sbarry753/cse123/max78000/README.md

# MAX78000 Platform Testing

Testing MAX78000FTHR as alternative platform for real-time polyphonic detection.

## Status
- Development environment: Set up complete
- Example code: Located and studied complete
- Hardware: Obtaining this week in progress
- Testing: Pending hardware in progress

## Examples
- `examples/I2S_DMA/` - Reference code for audio passthrough implementation

## Next Steps
1. Flash example to board when hardware arrives
2. Modify for audio passthrough
3. Benchmark performance
4. Compare to other results
