sbarry753/cse123/Documentation/aesthetic_prototype/topDownView.png

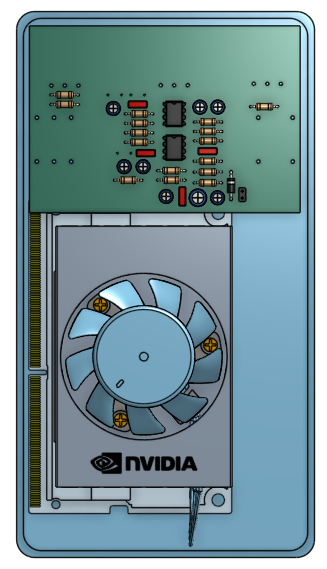
Documentation/aesthetic_prototype/topDownView.png
