sbarry753/cse123/Documentation/images/Guitar Pedal.drawio.png

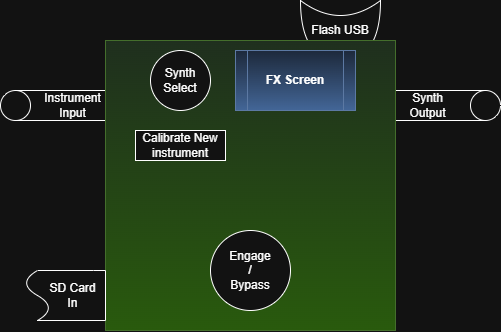
Documentation/images/Guitar Pedal.drawio.png
