sbarry753/cse123/Documentation/images/LUTPolyphonic.drawio (1).png

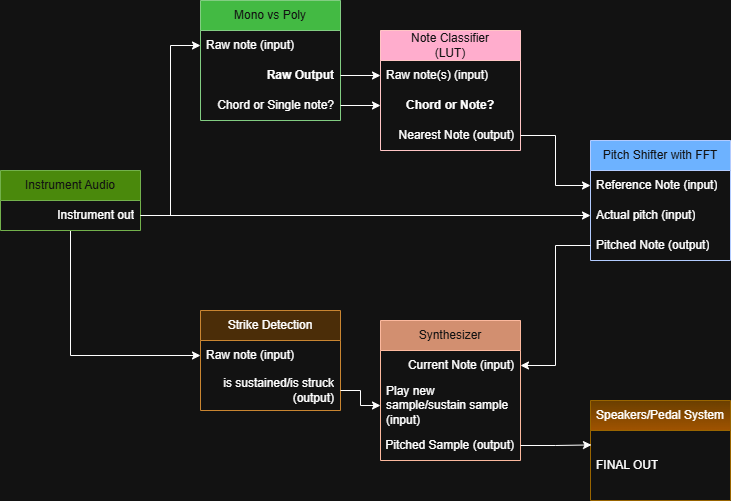
Documentation/images/LUTPolyphonic.drawio (1).png
