sbarry753/cse123/Documentation/images/pcm_signal.png

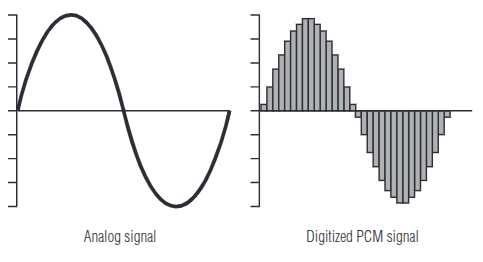
Documentation/images/pcm_signal.png
