sbarry753/cse123/Documentation/images/pedalAsciiArt.png

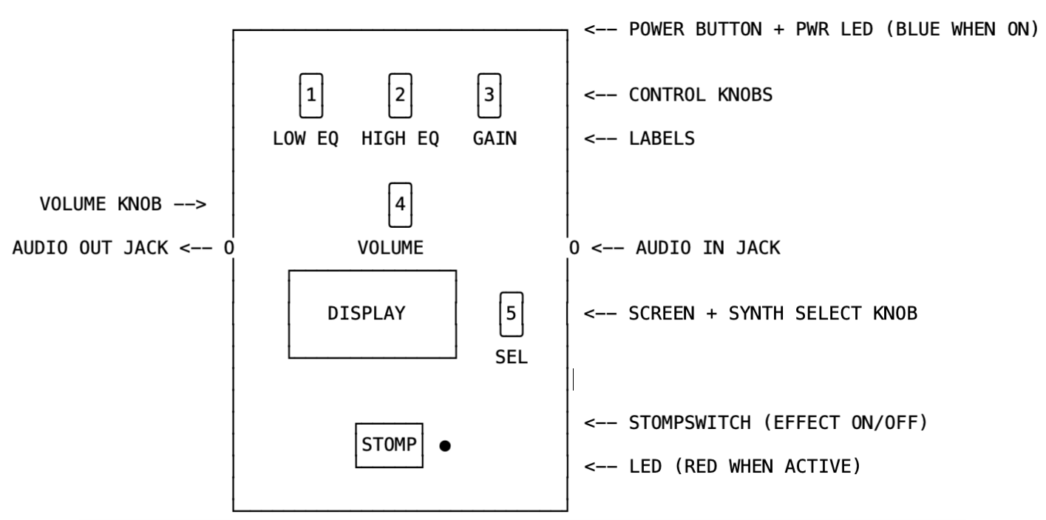
Documentation/images/pedalAsciiArt.png
