sbarry753/cse123/LUT - In Development/Notes on guitar.png

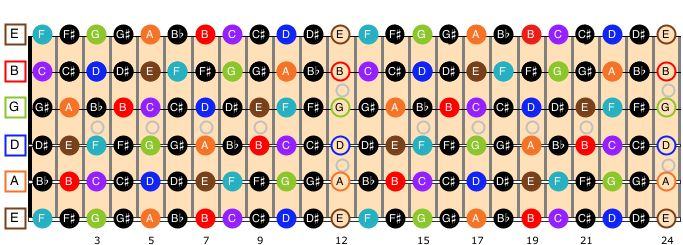
LUT - In Development/Notes on guitar.png
