sbarry753/cse123/NET - In Development/semitone_comparison.png

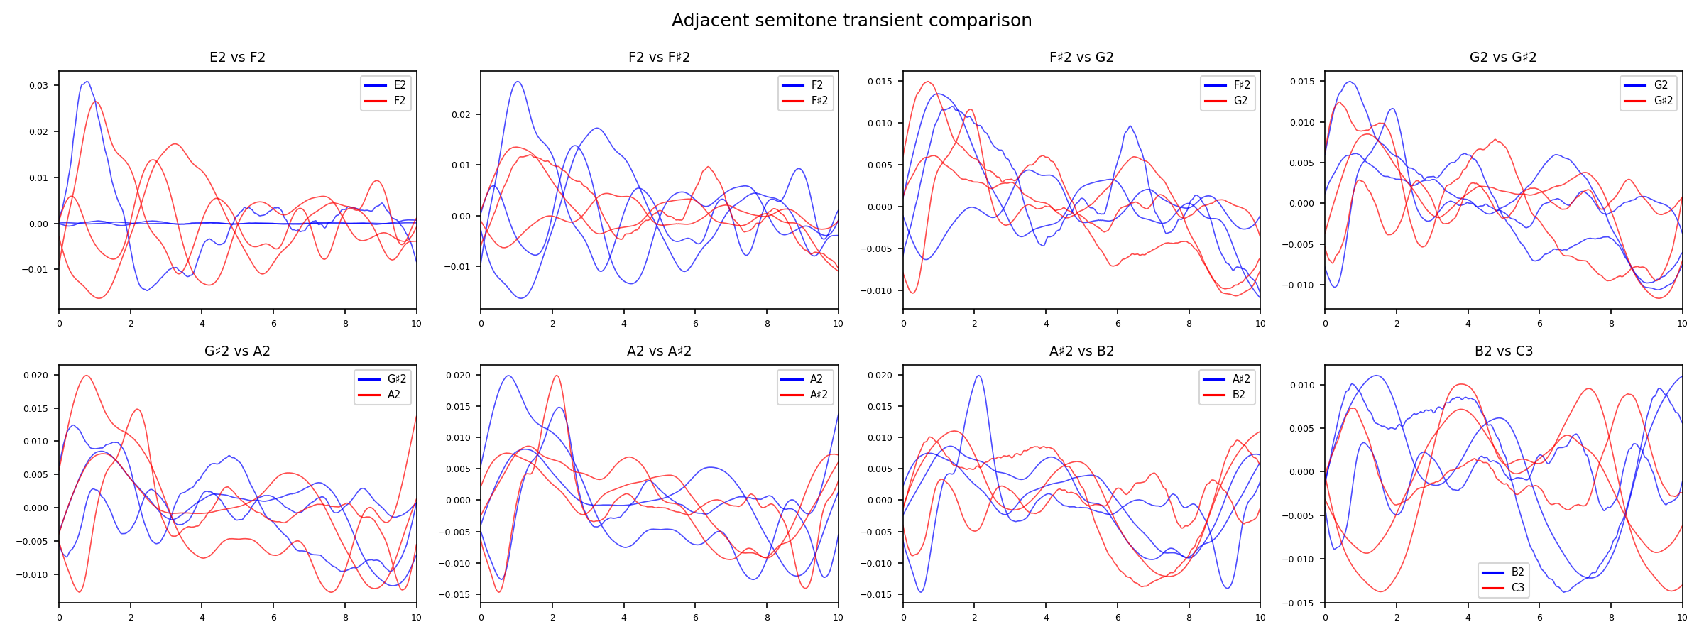
NET - In Development/semitone_comparison.png
