sbarry753/cse123/NET - In Development/transient_inspection.png

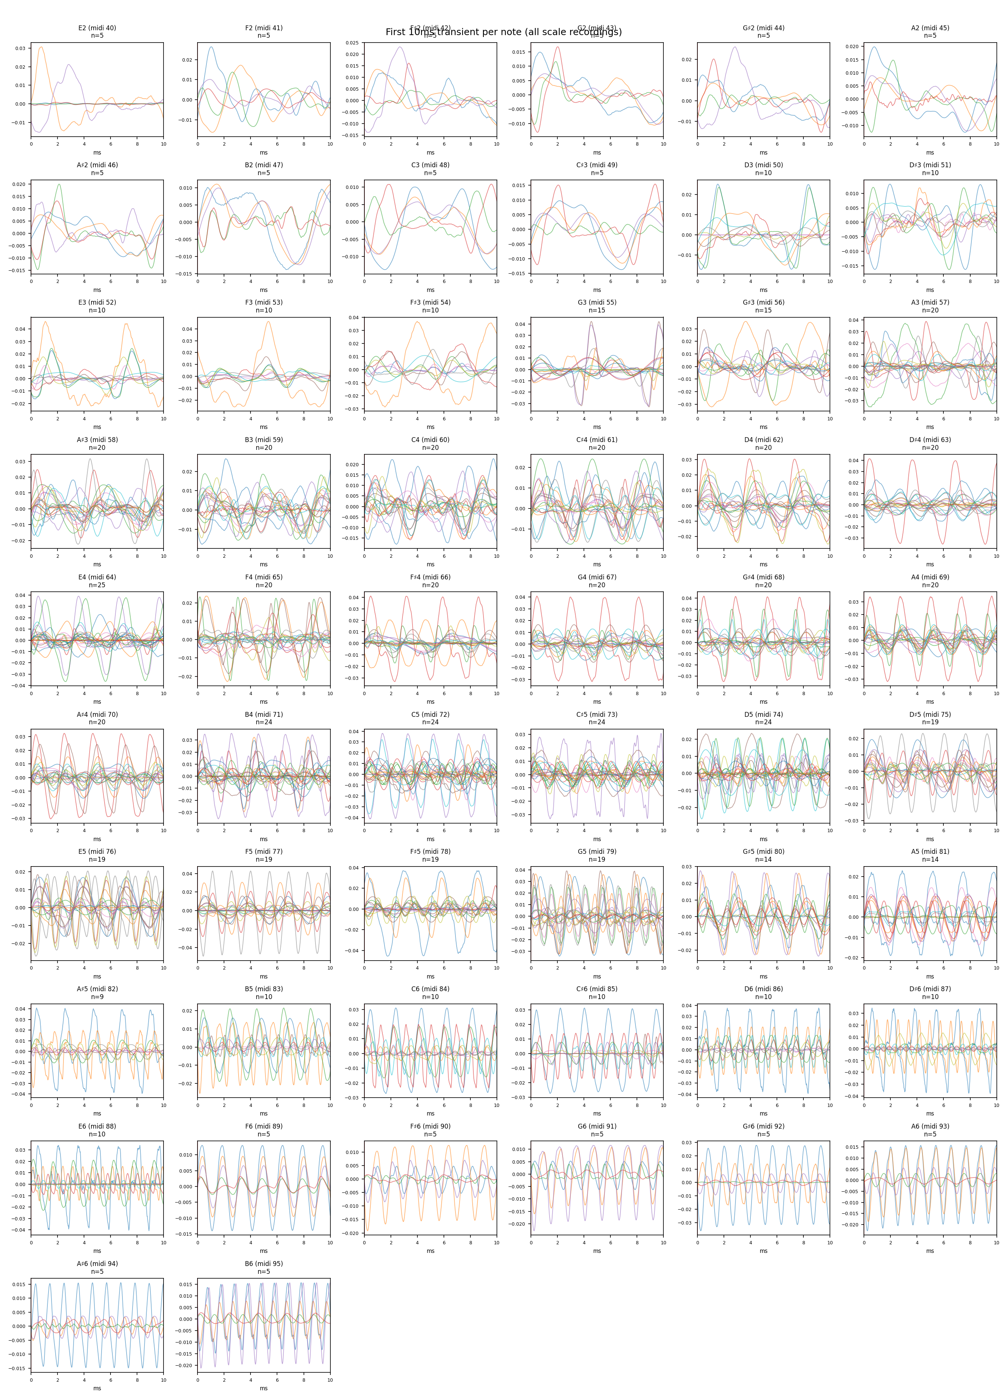
NET - In Development/transient_inspection.png
