sbarry753/cse123/special_effects/test_files/Downloads/LUTPolyphonic.drawio.png

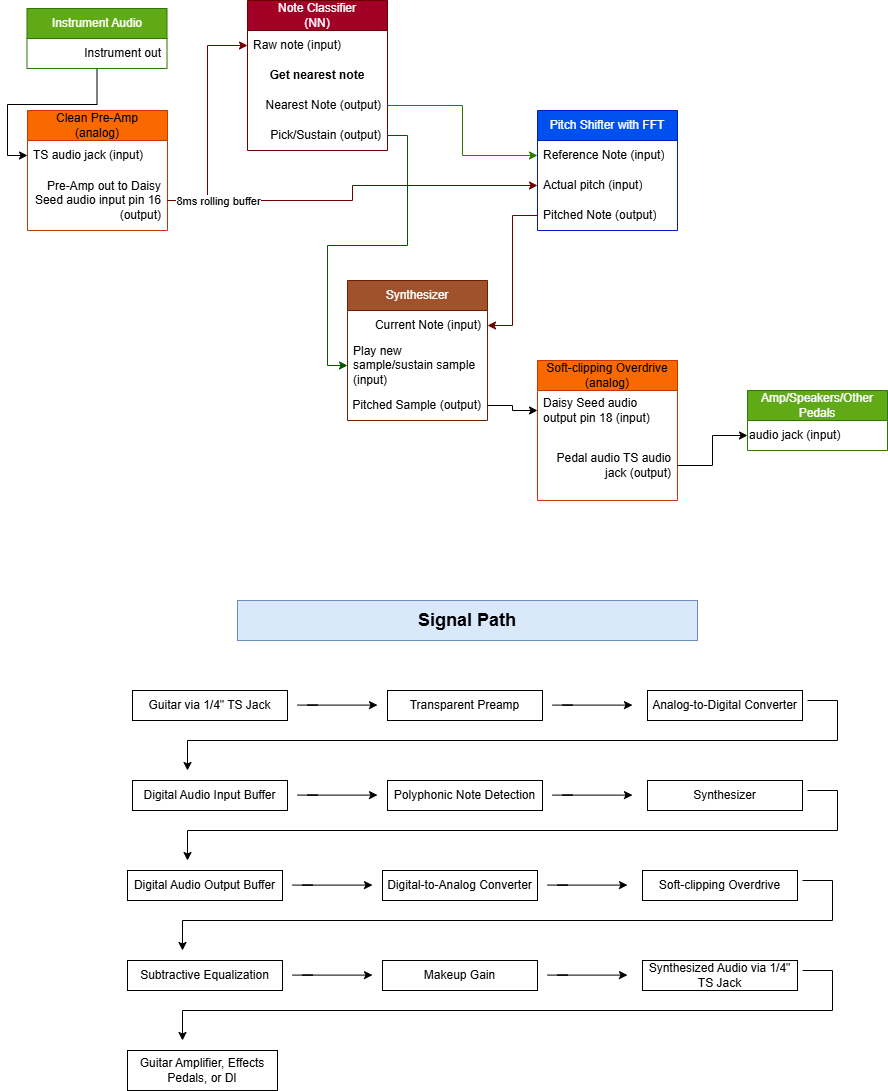
special_effects/test_files/Downloads/LUTPolyphonic.drawio.png
