sbarry753/cse123/special_effects/test_files/waveform_comparison.png

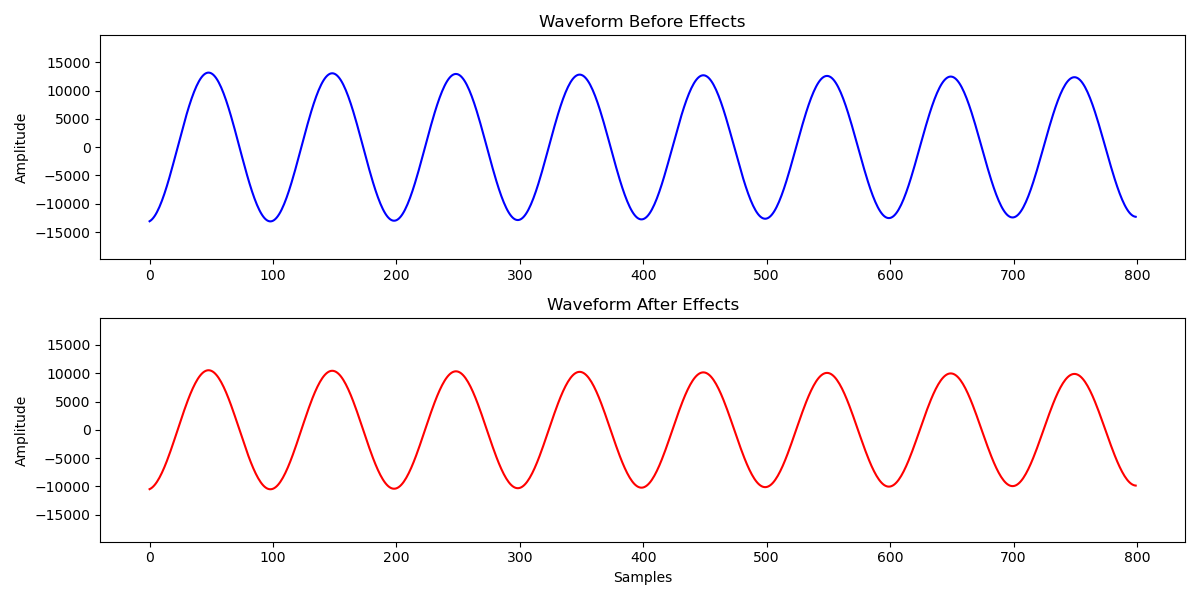
special_effects/test_files/waveform_comparison.png
