sbarry753/cse123/Analog/eq/eq.kicad_pcb

## KiCad design Analog/eq/eq.kicad_pcb (2026-04-29)

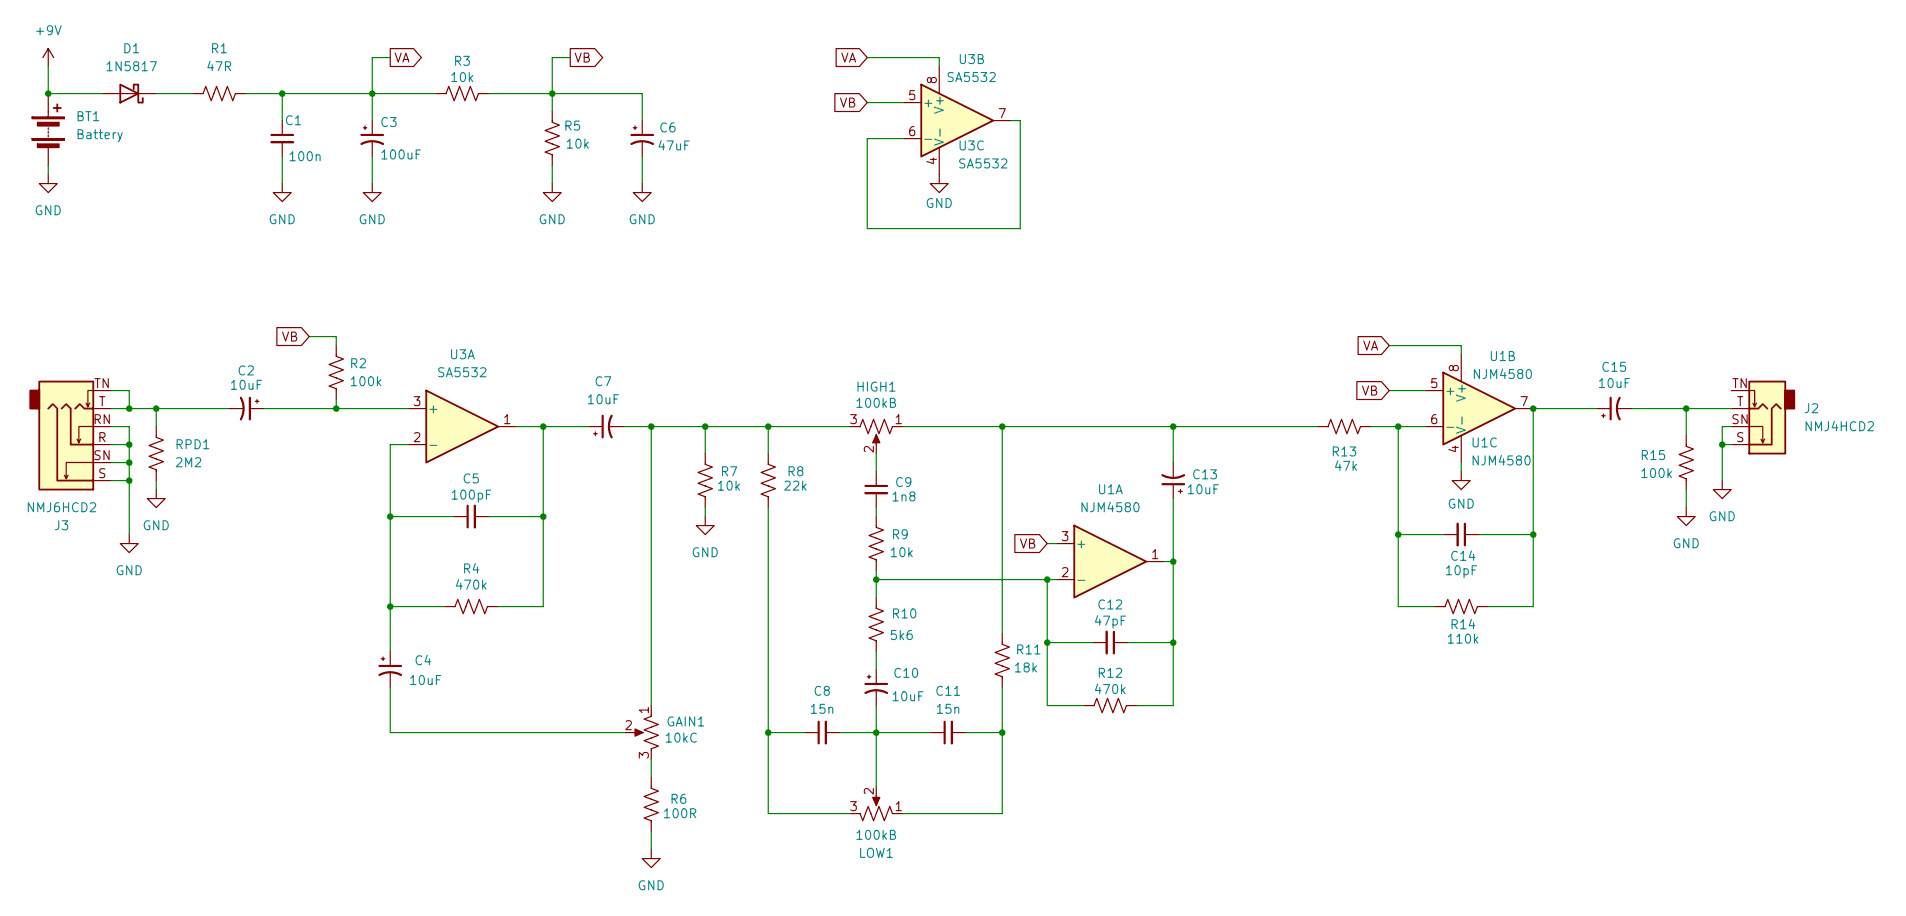
[picture p51: schematic eq.kicad_sch]

Parts:
BT1: Battery; PinHeader_1x02_P2.54mm_Vertical
C1: 100n; C_Rect_L7.0mm_W2.5mm_P5.00mm
C2, C4, C7, C10, C13, C15: 10uF; C_Radial_D5.0mm_H11.0mm_P2.00mm
C3: 100uF; C_Radial_D6.3mm_H11.0mm_P2.50mm
C5: 100pF; C_Rect_L7.0mm_W2.5mm_P5.00mm
C6: 47uF; C_Radial_D5.0mm_H11.0mm_P2.00mm
C8, C11: 15n; C_Rect_L7.2mm_W2.5mm_P5.00mm
C9: 1n8; C_Rect_L7.2mm_W2.5mm_P5.00mm
C12: 47pF; C_Rect_L7.0mm_W2.5mm_P5.00mm
C14: 10pF; C_Rect_L7.0mm_W2.5mm_P5.00mm
D1: 1N5817; D_DO-41_SOD81_P10.16mm_Horizontal
GAIN1: 10kC; Potentiometer_Omeg_PC16BU_Vertical
HIGH1: 100kB; Potentiometer_Omeg_PC16BU_Vertical
J2: NMJ4HCD2; Jack_6.35mm_Neutrik_NMJ4HCD2_Horizontal
J3: NMJ6HCD2; Jack_6.35mm_Neutrik_NMJ6HCD2_Horizontal
LOW1: 100kB; Potentiometer_Omeg_PC16BU_Vertical
R1: 47R; R_Axial_DIN0207_L6.3mm_D2.5mm_P10.16mm_Horizontal
R2, R15: 100k; R_Axial_DIN0207_L6.3mm_D2.5mm_P10.16mm_Horizontal
R3, R5, R7, R9: 10k; R_Axial_DIN0207_L6.3mm_D2.5mm_P10.16mm_Horizontal
R4, R12: 470k; R_Axial_DIN0207_L6.3mm_D2.5mm_P10.16mm_Horizontal
R6: 100R; R_Axial_DIN0207_L6.3mm_D2.5mm_P10.16mm_Horizontal
R8: 22k; R_Axial_DIN0207_L6.3mm_D2.5mm_P10.16mm_Horizontal
R10: 5k6; R_Axial_DIN0207_L6.3mm_D2.5mm_P10.16mm_Horizontal
R11: 18k; R_Axial_DIN0207_L6.3mm_D2.5mm_P10.16mm_Horizontal
R13: 47k; R_Axial_DIN0207_L6.3mm_D2.5mm_P10.16mm_Horizontal
R14: 110k; R_Axial_DIN0207_L6.3mm_D2.5mm_P10.16mm_Horizontal
RPD1: 2M2; R_Axial_DIN0207_L6.3mm_D2.5mm_P10.16mm_Horizontal
U1: NJM4580; DIP-8_W7.62mm_LongPads
U3: SA5532; DIP-8_W7.62mm_LongPads

Connections:
+9V: BT1.1 (+), D1.2 (A)
GND: BT1.2 (-), C1.2, C3.2, C6.2, J2.S, J2.SN, J3.R, J3.RN, J3.S, J3.SN, R5.2, R6.2, R7.2, R15.2, RPD1.2, U1.4 (V-), U3.4 (V-)
unnamed: C2.2, J3.T, J3.TN, RPD1.1
unnamed: C4.2, GAIN1.2
unnamed: C5.2, C7.1, R4.2, U3.1
unnamed: C7.2, GAIN1.1, HIGH1.3, R7.1, R8.1
unnamed: C8.1, LOW1.3, R8.2
unnamed: C9.1, HIGH1.2
unnamed: C9.2, R9.1
unnamed: C10.1, R10.2
unnamed: C8.2, C10.2, C11.1, LOW1.2
unnamed: C11.2, LOW1.1, R11.2
unnamed: C12.1, C13.1, R12.1, U1.1
unnamed: C13.2, HIGH1.1, R11.1, R13.2
unnamed: C14.1, C15.1, R14.1, U1.7
unnamed: C15.2, J2.T, R15.1
unnamed: D1.1 (K), R1.1
unnamed: GAIN1.3, R6.1
unnamed: C12.2, R9.2, R10.1, R12.2, U1.2 (-)
unnamed: C14.2, R13.1, R14.2, U1.6 (-)
unnamed: C2.1, R2.2, U3.3 (+)
unnamed: C4.1, C5.1, R4.1, U3.2 (-)
unnamed: U3.6 (-), U3.7
VA: C1.1, C3.1, R1.2, R3.1, U1.8 (V+), U3.8 (V+)
VB: C6.1, R2.1, R3.2, R5.1, U1.3 (+), U1.5 (+), U3.5 (+)

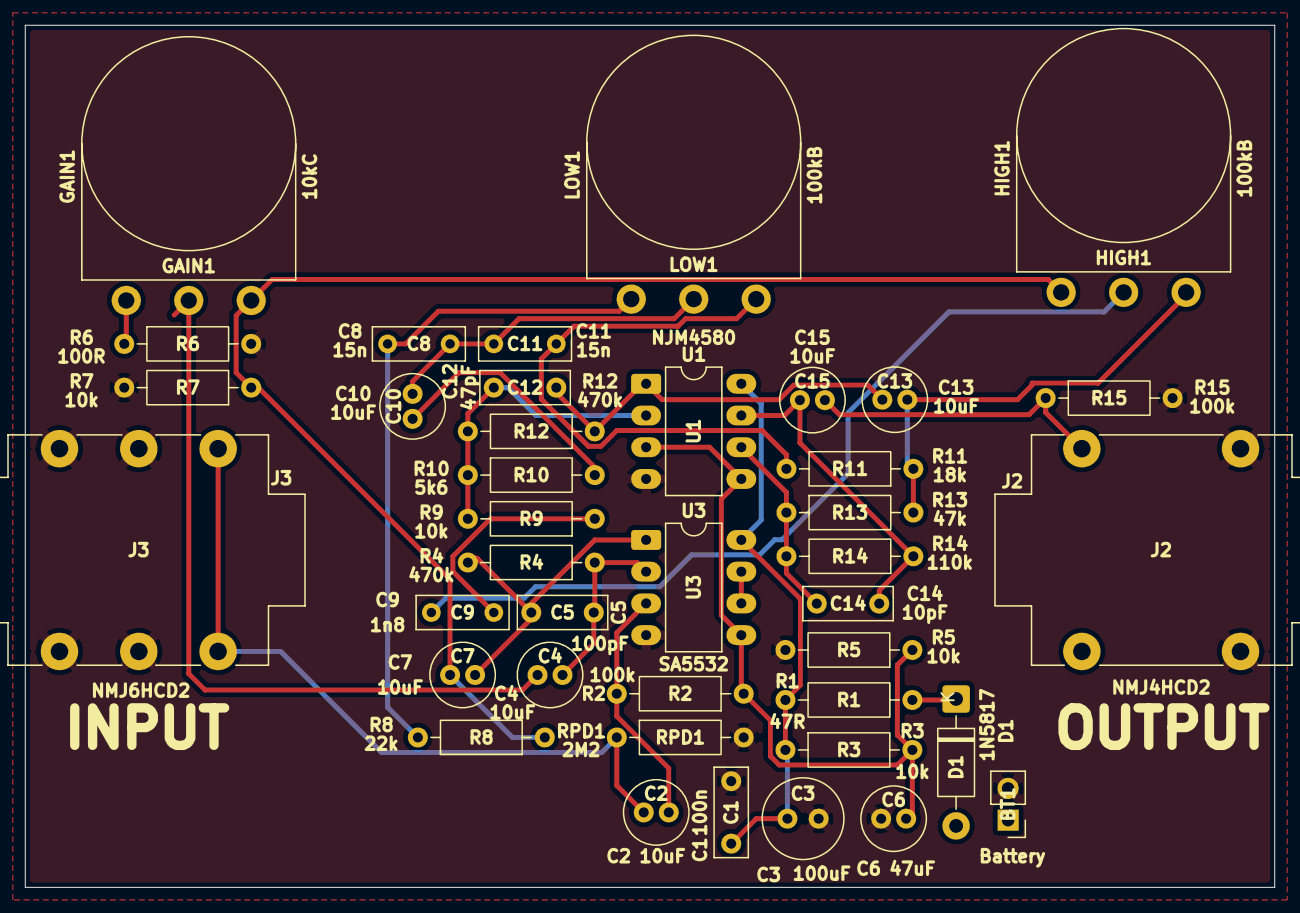
[picture p52: board eq.kicad_pcb from above]

Board: 2 copper layers, 100.0 x 69.0 mm, 40 parts (0 on the bottom side), 25 nets.
