sbarry753/cse123/Analog/preamp/preamp/preamp.kicad_pcb

## KiCad design Analog/preamp/preamp/preamp.kicad_pcb (2026-04-28)

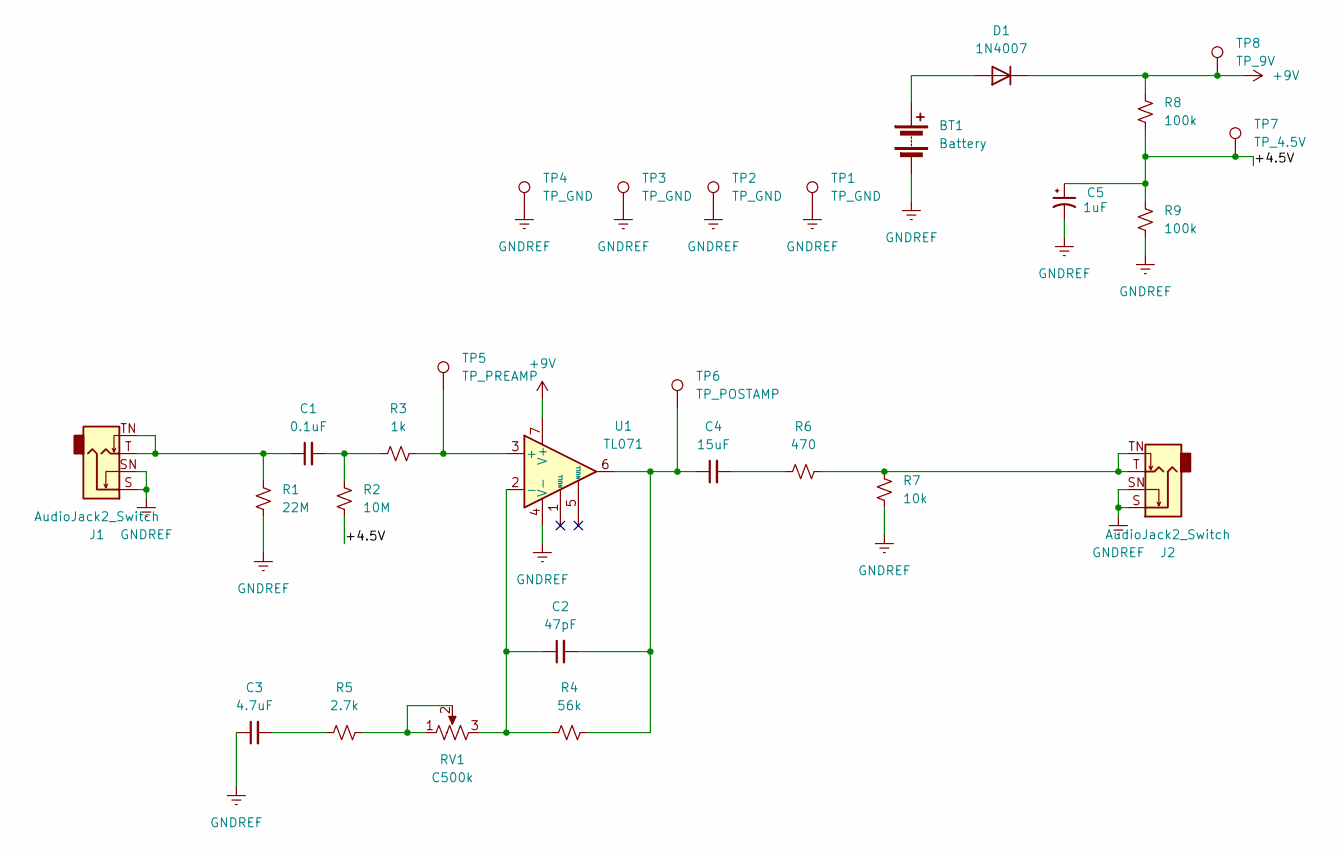
[picture p53: schematic preamp.kicad_sch]

Parts:
BT1: Battery; PinSocket_1x02_P2.54mm_Vertical
C1: 0.1uF; CP_Radial_D8.0mm_P3.80mm
C2: 47pF; CP_Radial_D8.0mm_P3.80mm
C3: 4.7uF; CP_Radial_D8.0mm_P3.80mm
C4: 15uF; CP_Radial_D8.0mm_P3.80mm
C5: 1uF; CP_Radial_D8.0mm_P3.80mm
D1: 1N4007; D_DO-41_SOD81_P10.16mm_Horizontal
J1, J2: AudioJack2_Switch; Jack_6.35mm_Neutrik_NMJ4HCD2_Horizontal
R1: 22M; R_Axial_DIN0414_L11.9mm_D4.5mm_P15.24mm_Horizontal
R2: 10M; R_Axial_DIN0414_L11.9mm_D4.5mm_P15.24mm_Horizontal
R3: 1k; R_Axial_DIN0414_L11.9mm_D4.5mm_P15.24mm_Horizontal
R4: 56k; R_Axial_DIN0414_L11.9mm_D4.5mm_P15.24mm_Horizontal
R5: 2.7k; R_Axial_DIN0414_L11.9mm_D4.5mm_P15.24mm_Horizontal
R6: 470; R_Axial_DIN0414_L11.9mm_D4.5mm_P15.24mm_Horizontal
R7: 10k; R_Axial_DIN0414_L11.9mm_D4.5mm_P15.24mm_Horizontal
R8, R9: 100k; R_Axial_DIN0414_L11.9mm_D4.5mm_P15.24mm_Horizontal
RV1: C500k; Potentiometer_Alpha_RD901F-40-00D_Single_Vertical
TP1, TP2, TP3, TP4: TP_GND; TestPoint_Loop_D3.50mm_Drill0.9mm_Beaded
TP5: TP_PREAMP; TestPoint_Loop_D3.50mm_Drill0.9mm_Beaded
TP6: TP_POSTAMP; TestPoint_Loop_D3.50mm_Drill0.9mm_Beaded
TP7: TP_4.5V; TestPoint_Loop_D3.50mm_Drill0.9mm_Beaded
TP8: TP_9V
U1: TL071; DIP-8_W7.62mm_LongPads

Connections:
+9V: D1.1 (K), R8.1, TP8.1, U1.7 (V+)
/+4.5V: C5.1, R2.2, R8.2, R9.1, TP7.1 (1_1)
GNDREF: BT1.2 (-), C3.1, C5.2, J1.S, J1.SN, J2.S, J2.SN, R1.2, R7.2, R9.2, TP1.1 (1_1), TP2.1 (1_1), TP3.1 (1_1), TP4.1 (1_1), U1.4 (V-)
unnamed: BT1.1 (+), D1.2 (A)
unnamed: C1.1, J1.T, J1.TN, R1.1
unnamed: C1.2, R2.1, R3.1
unnamed: C2.2, C4.1, R4.2, TP6.1 (1_1), U1.6
unnamed: C3.2, R5.1
unnamed: C4.2, R6.1
unnamed: J2.T, J2.TN, R6.2, R7.1
unnamed: R5.2, RV1.1, RV1.2
unnamed: R3.2, TP5.1 (1_1), U1.3 (+)
unnamed: C2.1, R4.1, RV1.3, U1.2 (-)

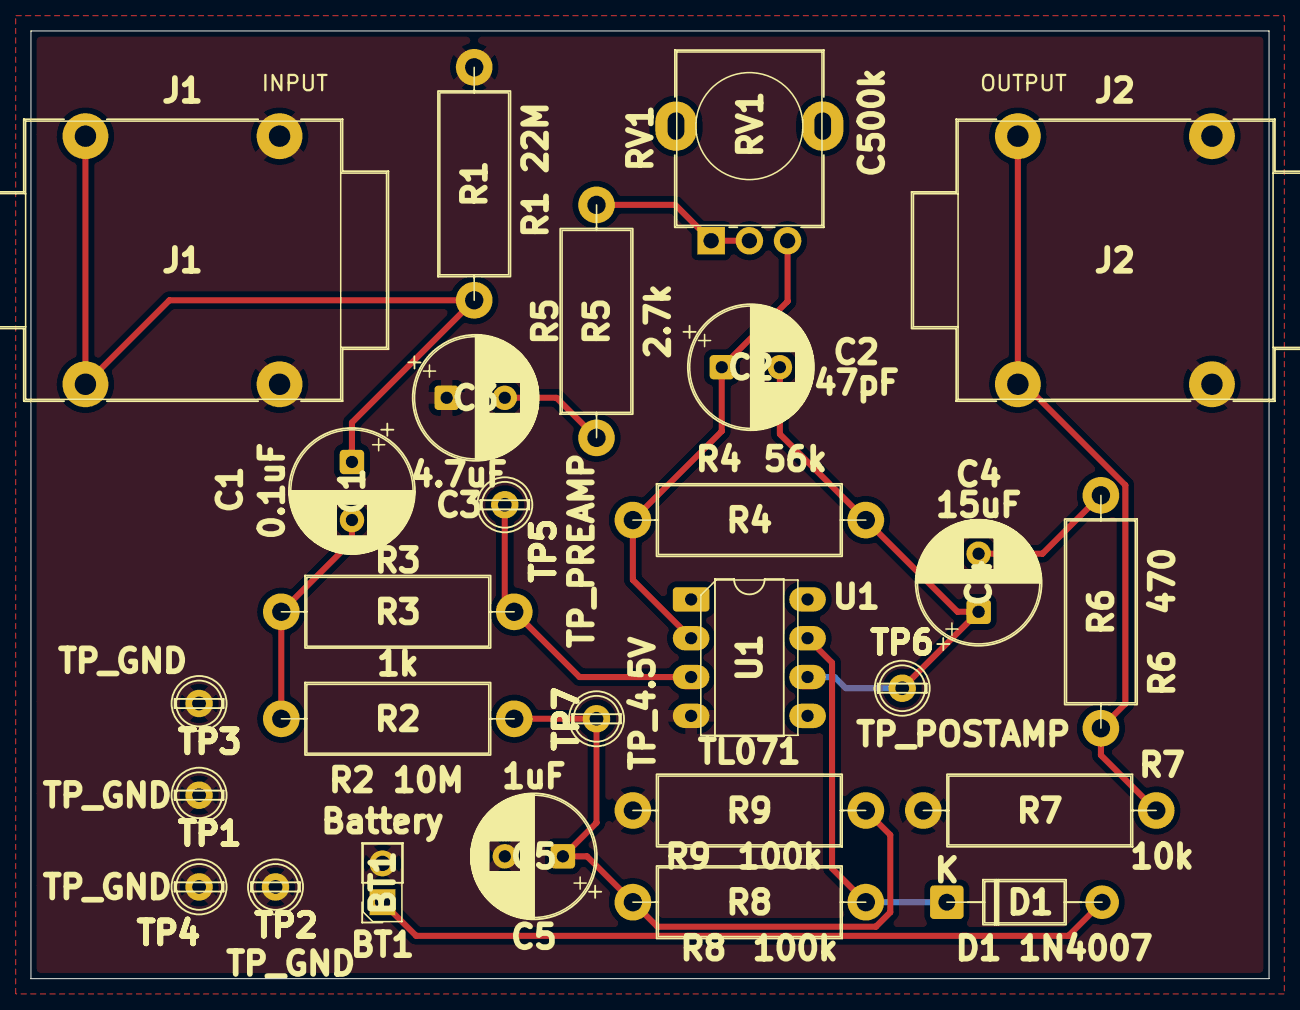
[picture p54: board preamp.kicad_pcb from above]

Board: 2 copper layers, 81.0 x 62.0 mm, 27 parts (0 on the bottom side), 13 nets.
