sbarry753/cse123/Analog/wamp_overdrive/wamp_overdrive.kicad_pcb

## KiCad design Analog/wamp_overdrive/wamp_overdrive.kicad_pcb (2026-02-23)

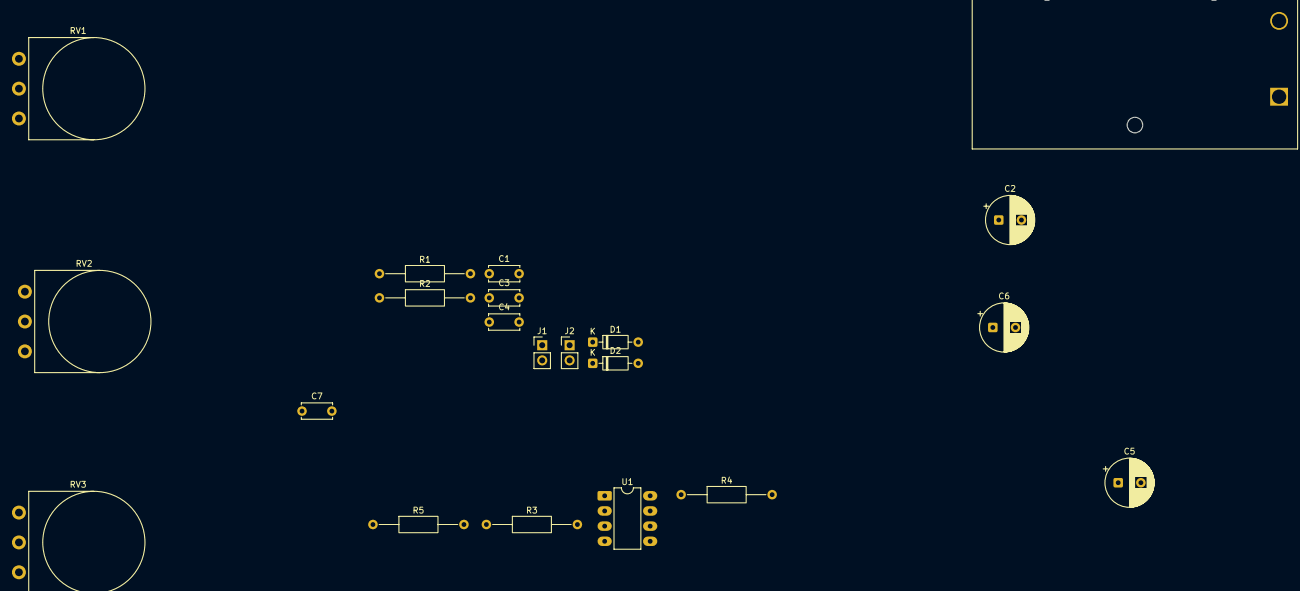
[picture p55: board wamp_overdrive.kicad_pcb from above]

Board: 2 copper layers, 21 parts (0 on the bottom side), 11 nets, no tracks yet.

Parts:
BT1: Battery; BatteryHolder_Eagle_12BH611-GR
C1: 470nF; C_Disc_D5.0mm_W2.5mm_P5.00mm
C2, C6: 47uF; CP_Radial_D8.0mm_P3.80mm
C3: 220nF; C_Disc_D5.0mm_W2.5mm_P5.00mm
C4: 100pF; C_Disc_D5.0mm_W2.5mm_P5.00mm
C5: 1uF; CP_Radial_D8.0mm_P3.80mm
C7: 22nF; C_Disc_D5.0mm_W2.5mm_P5.00mm
D1, D2: 1N4148; D_DO-35_SOD27_P7.62mm_Horizontal
J1, J2: AudioJack2; PinHeader_1x02_P2.54mm_Vertical
R1, R2, R4: 10k; R_Axial_DIN0207_L6.3mm_D2.5mm_P15.24mm_Horizontal
R3: 1M; R_Axial_DIN0207_L6.3mm_D2.5mm_P15.24mm_Horizontal
R5: 1k; R_Axial_DIN0207_L6.3mm_D2.5mm_P15.24mm_Horizontal
RV1: 500k; Potentiometer_Omeg_PC16BU_Vertical
RV2: 10k; Potentiometer_Omeg_PC16BU_Vertical
RV3: 100k; Potentiometer_Omeg_PC16BU_Vertical
U1: TL082; DIP-8_W7.62mm_LongPads

Connections:
+9V: BT1.1 (+), C6.1, R4.1, U1.8 (V+)
GND: BT1.2 (-), C2.2, C3.2, C6.2, C7.1, R2.2, RV3.3, U1.4 (V-)
unnamed: C1.1, R1.2
unnamed: C2.1, R2.1, R3.1, R4.2
unnamed: C3.1, R5.2
unnamed: C5.1, RV2.3
unnamed: C7.2, RV2.2
unnamed: C4.1, D1.2 (A), D2.1 (K), R5.1, RV1.3, U1.2 (-)
unnamed: C4.2, C5.2, D1.1 (K), D2.2 (A), RV1.1, RV1.2, U1.1
unnamed: RV2.1, RV3.1
unnamed: C1.2, R3.2, U1.3 (+)
