sbarry753/cse123/max78000_timbre_transfer/gusynth/main.c

/*******************************************************************************
* Copyright (C) 2019-2024 Maxim Integrated Products, Inc., All rights Reserved.
*
* This software is protected by copyright laws of the United States and
* of foreign countries. This material may also be protected by patent laws
* and technology transfer regulations of the United States and of foreign
* countries. This software is furnished under a license agreement and/or a
* nondisclosure agreement and may only be used or reproduced in accordance
* with the terms of those agreements. Dissemination of this information to
* any party or parties not specified in the license agreement and/or
* nondisclosure agreement is expressly prohibited.
*
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
* Except as contained in this notice, the name of Maxim Integrated
* Products, Inc. shall not be used except as stated in the Maxim Integrated
* Products, Inc. Branding Policy.
*
* The mere transfer of this software does not imply any licenses
* of trade secrets, proprietary technology, copyrights, patents,
* trademarks, maskwork rights, or any other form of intellectual
* property whatsoever. Maxim Integrated Products, Inc. retains all
* ownership rights.
*******************************************************************************/

// gusynth
// This file was @generated by ai8xize.py --device MAX78000 --config-file ../../max78000_timbre_transfer/timbre_student.yaml --checkpoint-file ../../max78000_timbre_transfer/checkpoints/q8_best.pth.tar --prefix gusynth --board-name FTHR_RevA --sample-input tests/sample_MAXGuitarPiano.npy --test-dir ../../max78000_timbre_transfer/ --overwrite

#include <stdlib.h>
#include <stdint.h>
#include <string.h>
#include <stdio.h>
#include "mxc.h"
#include "cnn.h"
#include "sampledata.h"
#include "sampleoutput.h"

volatile uint32_t cnn_time; // Stopwatch

void fail(void)
{
  printf("\n*** FAIL ***\n\n");
  while (1);
}

// 1-channel 513x5 data input (2565 bytes / 642 32-bit words):
// CHW 513x5, channel 0
static const uint32_t input_0[] = SAMPLE_INPUT_0;

void load_input(void)
{
  // This function loads the sample data input -- replace with actual data

  memcpy32((uint32_t *) 0x50400000, input_0, 642);
}

// Expected output of layer 4 for gusynth given the sample input (known-answer test)
// Delete this function for production code
static const uint32_t sample_output[] = SAMPLE_OUTPUT;
int check_output(void)
{
  int i;
  uint32_t mask, len;
  volatile uint32_t *addr;
  const uint32_t *ptr = sample_output;

  while ((addr = (volatile uint32_t *) *ptr++) != 0) {
    mask = *ptr++;
    len = *ptr++;
    for (i = 0; i < len; i++)
      if ((*addr++ & mask) != *ptr++) {
        printf("Data mismatch (%d/%d) at address 0x%08x: Expected 0x%08x, read 0x%08x.\n",
               i + 1, len, addr - 1, *(ptr - 1), *(addr - 1) & mask);
        return CNN_FAIL;
      }
  }

  return CNN_OK;
}

static int32_t ml_data[CNN_NUM_OUTPUTS];

int main(void)
{
  MXC_ICC_Enable(MXC_ICC0); // Enable cache

  // Switch to 100 MHz clock
  MXC_SYS_Clock_Select(MXC_SYS_CLOCK_IPO);
  SystemCoreClockUpdate();

  printf("Waiting...\n");

  // DO NOT DELETE THIS LINE:
  MXC_Delay(SEC(2)); // Let debugger interrupt if needed

  // Enable peripheral, enable CNN interrupt, turn on CNN clock
  // CNN clock: APB (50 MHz) div 1
  cnn_enable(MXC_S_GCR_PCLKDIV_CNNCLKSEL_PCLK, MXC_S_GCR_PCLKDIV_CNNCLKDIV_DIV1);

  printf("\n*** CNN Inference Test gusynth ***\n");

  // Measure setup/start overhead (init, load, configure, input load, start call).
  // MXC_TMR_SW_Start(MXC_TMR1);
  
  cnn_init(); // Bring state machine into consistent state
  cnn_load_weights(); // Load kernels
  cnn_load_bias();
  cnn_configure(); // Configure state machine
  load_input(); // Load data input
  cnn_start(); // Start CNN processing

  // uint32_t setup_time_us = MXC_TMR_SW_Stop(MXC_TMR1);
  // printf("Setup+start time: %u us\n", setup_time_us);

  while (cnn_time == 0)
    MXC_LP_EnterSleepMode(); // Wait for CNN

  if (check_output() != CNN_OK) fail();
  cnn_unload((uint32_t *) ml_data);

  printf("\n*** PASS ***\n\n");

#ifdef CNN_INFERENCE_TIMER
  printf("Approximate inference time: %u us\n\n", cnn_time);
#endif

  cnn_disable(); // Shut down CNN clock, disable peripheral


  return 0;
}

/*
  SUMMARY OF OPS
  Hardware: 12,147,840 ops (12,024,720 macc; 123,120 comp; 0 add; 0 mul; 0 bitwise)
    Layer 0: 205,200 ops (184,680 macc; 20,520 comp; 0 add; 0 mul; 0 bitwise)
    Layer 1: 2,995,920 ops (2,954,880 macc; 41,040 comp; 0 add; 0 mul; 0 bitwise)
    Layer 2: 5,950,800 ops (5,909,760 macc; 41,040 comp; 0 add; 0 mul; 0 bitwise)
    Layer 3: 2,975,400 ops (2,954,880 macc; 20,520 comp; 0 add; 0 mul; 0 bitwise)
    Layer 4: 20,520 ops (20,520 macc; 0 comp; 0 add; 0 mul; 0 bitwise)

  RESOURCE USAGE
  Weight memory: 4,688 bytes out of 442,368 bytes total (1.1%)
  Bias memory:   49 bytes out of 2,048 bytes total (2.4%)
*/
