sbarry753/cse123/max78000_timbre_transfer/gusynth/cnn.c

/*******************************************************************************
* Copyright (C) 2019-2024 Maxim Integrated Products, Inc., All rights Reserved.
*
* This software is protected by copyright laws of the United States and
* of foreign countries. This material may also be protected by patent laws
* and technology transfer regulations of the United States and of foreign
* countries. This software is furnished under a license agreement and/or a
* nondisclosure agreement and may only be used or reproduced in accordance
* with the terms of those agreements. Dissemination of this information to
* any party or parties not specified in the license agreement and/or
* nondisclosure agreement is expressly prohibited.
*
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
* Except as contained in this notice, the name of Maxim Integrated
* Products, Inc. shall not be used except as stated in the Maxim Integrated
* Products, Inc. Branding Policy.
*
* The mere transfer of this software does not imply any licenses
* of trade secrets, proprietary technology, copyrights, patents,
* trademarks, maskwork rights, or any other form of intellectual
* property whatsoever. Maxim Integrated Products, Inc. retains all
* ownership rights.
*******************************************************************************/

// gusynth
// This file was @generated by ai8xize.py --device MAX78000 --config-file ../../max78000_timbre_transfer/timbre_student.yaml --checkpoint-file ../../max78000_timbre_transfer/checkpoints/q8_best.pth.tar --prefix gusynth --board-name FTHR_RevA --sample-input tests/sample_MAXGuitarPiano.npy --test-dir ../../max78000_timbre_transfer/ --overwrite

// DO NOT EDIT - regenerate this file instead!

// Configuring 5 layers
// Input data: CHW
// Layer 0: 1x513x5, no pooling, conv2d with kernel size 3x3, stride 1/1, pad 1/1, ReLU, 8x513x5 output
// Layer 1: 8x513x5, no pooling, conv2d with kernel size 3x3, stride 1/1, pad 1/1, ReLU, 16x513x5 output
// Layer 2: 16x513x5, no pooling, conv2d with kernel size 3x3, stride 1/1, pad 1/1, ReLU, 16x513x5 output
// Layer 3: 16x513x5, no pooling, conv2d with kernel size 3x3, stride 1/1, pad 1/1, ReLU, 8x513x5 output
// Layer 4: 8x513x5, no pooling, conv2d with kernel size 1x1, stride 1/1, pad 0/0, no activation, 1x513x5 output

// Final Scales: {0: 0, 1: 0, 2: 0, 3: 0, 4: 0}

#include <stdlib.h>
#include <stdint.h>
#include <string.h>
#include <stdio.h>
#include "mxc.h"
#include "gcfr_regs.h"
#include "cnn.h"
#include "weights.h"

void CNN_ISR(void)
{
  // Acknowledge interrupt to all quadrants
  *((volatile uint32_t *) 0x50100000) &= ~((1<<12) | 1);

  CNN_COMPLETE; // Signal that processing is complete
#ifdef CNN_INFERENCE_TIMER
  cnn_time = MXC_TMR_SW_Stop(CNN_INFERENCE_TIMER);
#else
  cnn_time = 1;
#endif
}

int cnn_continue(void)
{
  cnn_time = 0;

  *((volatile uint32_t *) 0x50100000) |= 1; // Re-enable quadrant 0

  return CNN_OK;
}

int cnn_stop(void)
{
  *((volatile uint32_t *) 0x50100000) &= ~1; // Disable quadrant 0

  return CNN_OK;
}

void memcpy32(uint32_t *dst, const uint32_t *src, int n)
{
  while (n-- > 0) {
    *dst++ = *src++;
  }
}

static const uint32_t kernels[] = KERNELS;

int cnn_load_weights(void)
{
  uint32_t len;
  volatile uint32_t *addr;
  const uint32_t *ptr = kernels;

  while ((addr = (volatile uint32_t *) *ptr++) != 0) {
    *((volatile uint8_t *) ((uint32_t) addr | 1)) = 0x01; // Set address
    len = *ptr++;
    while (len-- > 0)
      *addr++ = *ptr++;
  }

  return CNN_OK;
}

static const uint8_t bias_0[] = BIAS_0;

static void memcpy_8to32(uint32_t *dst, const uint8_t *src, int n)
{
  while (n-- > 0) {
    *dst++ = *src++;
  }
}

int cnn_load_bias(void)
{
  memcpy_8to32((uint32_t *) 0x50108000, bias_0, sizeof(uint8_t) * 49);

  return CNN_OK;
}

int cnn_init(void)
{
  *((volatile uint32_t *) 0x50001000) = 0x00000000; // AON control
  *((volatile uint32_t *) 0x50100000) = 0x00100008; // Stop SM
  *((volatile uint32_t *) 0x50100004) = 0x0000040e; // SRAM control
  *((volatile uint32_t *) 0x50100008) = 0x00000004; // Layer count

  return CNN_OK;
}

int cnn_configure(void)
{
  // Layer 0 quadrant 0
  *((volatile uint32_t *) 0x50100010) = 0x00010202; // Rows
  *((volatile uint32_t *) 0x50100090) = 0x00010006; // Columns
  *((volatile uint32_t *) 0x50100310) = 0x00001000; // SRAM write ptr
  *((volatile uint32_t *) 0x50100410) = 0x00002000; // Write ptr mask offs
  *((volatile uint32_t *) 0x50100590) = 0x00000b60; // Layer control
  *((volatile uint32_t *) 0x50100a10) = 0x00003800; // Layer control 2
  *((volatile uint32_t *) 0x50100610) = 0x00000038; // Mask offset and count
  *((volatile uint32_t *) 0x50100690) = 0x00000004; // TRAM ptr max
  *((volatile uint32_t *) 0x50100790) = 0x00003000; // Post processing register
  *((volatile uint32_t *) 0x50100710) = 0x00010001; // Mask and processor enables

  // Layer 1 quadrant 0
  *((volatile uint32_t *) 0x50100014) = 0x00010202; // Rows
  *((volatile uint32_t *) 0x50100094) = 0x00010006; // Columns
  *((volatile uint32_t *) 0x50100414) = 0x00002000; // Write ptr mask offs
  *((volatile uint32_t *) 0x50100514) = 0x00001000; // SRAM read ptr
  *((volatile uint32_t *) 0x50100594) = 0x00000b20; // Layer control
  *((volatile uint32_t *) 0x50100a14) = 0x00007800; // Layer control 2
  *((volatile uint32_t *) 0x50100614) = 0x004000b8; // Mask offset and count
  *((volatile uint32_t *) 0x50100694) = 0x00000004; // TRAM ptr max
  *((volatile uint32_t *) 0x50100794) = 0x00001008; // Post processing register
  *((volatile uint32_t *) 0x50100714) = 0x00ff00ff; // Mask and processor enables

  // Layer 2 quadrant 0
  *((volatile uint32_t *) 0x50100018) = 0x00010202; // Rows
  *((volatile uint32_t *) 0x50100098) = 0x00010006; // Columns
  *((volatile uint32_t *) 0x50100318) = 0x00001000; // SRAM write ptr
  *((volatile uint32_t *) 0x50100418) = 0x00002000; // Write ptr mask offs
  *((volatile uint32_t *) 0x50100598) = 0x00000b20; // Layer control
  *((volatile uint32_t *) 0x50100a18) = 0x00007800; // Layer control 2
  *((volatile uint32_t *) 0x50100618) = 0x00c00138; // Mask offset and count
  *((volatile uint32_t *) 0x50100698) = 0x00000004; // TRAM ptr max
  *((volatile uint32_t *) 0x50100798) = 0x00023018; // Post processing register
  *((volatile uint32_t *) 0x50100718) = 0xffffffff; // Mask and processor enables

  // Layer 3 quadrant 0
  *((volatile uint32_t *) 0x5010001c) = 0x00010202; // Rows
  *((volatile uint32_t *) 0x5010009c) = 0x00010006; // Columns
  *((volatile uint32_t *) 0x5010041c) = 0x00002000; // Write ptr mask offs
  *((volatile uint32_t *) 0x5010051c) = 0x00001000; // SRAM read ptr
  *((volatile uint32_t *) 0x5010059c) = 0x00000b20; // Layer control
  *((volatile uint32_t *) 0x50100a1c) = 0x00003800; // Layer control 2
  *((volatile uint32_t *) 0x5010061c) = 0x01400178; // Mask offset and count
  *((volatile uint32_t *) 0x5010069c) = 0x00000004; // TRAM ptr max
  *((volatile uint32_t *) 0x5010079c) = 0x00023028; // Post processing register
  *((volatile uint32_t *) 0x5010071c) = 0xffffffff; // Mask and processor enables

  // Layer 4 quadrant 0
  *((volatile uint32_t *) 0x50100020) = 0x00000200; // Rows
  *((volatile uint32_t *) 0x501000a0) = 0x00000004; // Columns
  *((volatile uint32_t *) 0x50100320) = 0x00001000; // SRAM write ptr
  *((volatile uint32_t *) 0x501003a0) = 0x00000001; // Write ptr time slot offs
  *((volatile uint32_t *) 0x50100420) = 0x00002000; // Write ptr mask offs
  *((volatile uint32_t *) 0x501005a0) = 0x00000920; // Layer control
  *((volatile uint32_t *) 0x50100620) = 0x0d800d80; // Mask offset and count
  *((volatile uint32_t *) 0x50100120) = 0x00000100; // 1D
  *((volatile uint32_t *) 0x501007a0) = 0x00001030; // Post processing register
  *((volatile uint32_t *) 0x50100720) = 0x00ff00ff; // Mask and processor enables


  return CNN_OK;
}

int cnn_start(void)
{
  cnn_time = 0;

  *((volatile uint32_t *) 0x50100000) = 0x00100808; // Enable quadrant 0

#ifdef CNN_INFERENCE_TIMER
  MXC_TMR_SW_Start(CNN_INFERENCE_TIMER);
#endif

  CNN_START; // Allow capture of processing time
  *((volatile uint32_t *) 0x50100000) = 0x00100009; // Master enable quadrant 0

  return CNN_OK;
}

int cnn_unload(uint32_t *out_buf32)
{
  uint16_t *out_buf = (uint16_t *) out_buf32;
  uint32_t val;
  volatile uint32_t *addr;
  int i;
  uint32_t offs;

  // Custom unload for this network, layer 4: 8-bit data, shape: (1, 513, 5)
  offs = 0x0000;
  addr = (volatile uint32_t *) 0x50404000;
  for (i = 0; i < 2565; i++) {
    val = *addr++;
    out_buf[offs] = (val & 0xff);
    offs++;
  }

  return CNN_OK;
}

int cnn_enable(uint32_t clock_source, uint32_t clock_divider)
{
  // Reset all domains, restore power to CNN
  MXC_GCFR->reg3 = 0xf; // Reset
  MXC_GCFR->reg1 = 0x1; // Mask memory
  MXC_GCFR->reg0 = 0x1; // Power
  MXC_GCFR->reg2 = 0xe; // Iso
  MXC_GCFR->reg3 = 0x0; // Reset

  MXC_GCR->pclkdiv = (MXC_GCR->pclkdiv & ~(MXC_F_GCR_PCLKDIV_CNNCLKDIV | MXC_F_GCR_PCLKDIV_CNNCLKSEL))
                     | clock_divider | clock_source;
  MXC_SYS_ClockEnable(MXC_SYS_PERIPH_CLOCK_CNN); // Enable CNN clock

  MXC_NVIC_SetVector(CNN_IRQn, CNN_ISR); // Set CNN complete vector

  return CNN_OK;
}

int cnn_boost_enable(mxc_gpio_regs_t *port, uint32_t pin)
{
  mxc_gpio_cfg_t gpio_out;
  gpio_out.port = port;
  gpio_out.mask = pin;
  gpio_out.pad = MXC_GPIO_PAD_NONE;
  gpio_out.func = MXC_GPIO_FUNC_OUT;
  MXC_GPIO_Config(&gpio_out);
  MXC_GPIO_OutSet(gpio_out.port, gpio_out.mask);

  return CNN_OK;
}

int cnn_boost_disable(mxc_gpio_regs_t *port, uint32_t pin)
{
  mxc_gpio_cfg_t gpio_out;
  gpio_out.port = port;
  gpio_out.mask = pin;
  gpio_out.pad = MXC_GPIO_PAD_NONE;
  gpio_out.func = MXC_GPIO_FUNC_OUT;
  MXC_GPIO_Config(&gpio_out);
  MXC_GPIO_OutClr(gpio_out.port, gpio_out.mask);

  return CNN_OK;
}

int cnn_disable(void)
{
  // Disable CNN clock
  MXC_SYS_ClockDisable(MXC_SYS_PERIPH_CLOCK_CNN);

  // Disable power to CNN
  MXC_GCFR->reg3 = 0xf; // Reset
  MXC_GCFR->reg2 |= 0xf; // Iso
  MXC_GCFR->reg0 = 0x0; // Power
  MXC_GCFR->reg1 = 0x0; // Mask memory
  MXC_GCFR->reg3 = 0x0; // Reset

  return CNN_OK;
}
