sbarry753/cse123/max78000_timbre_transfer/gusynth/sampleoutput.h

// This file was @generated automatically

#define SAMPLE_OUTPUT { \
  0x50404000, 0x000000ff, 0x00000a05, 0x0000007f, 0x0000007f, 0x0000007f, 0x0000007f, 0x0000007f, \
  0x0000007f, 0x0000007f, 0x0000007f, 0x0000007f, 0x0000007f, 0x0000007f, 0x0000007f, 0x0000007f, \
  0x0000007f, 0x0000007f, 0x0000007f, 0x0000007f, 0x0000007f, 0x0000007f, 0x0000007f, 0x0000007f, \
  0x0000007f, 0x0000007f, 0x0000007f, 0x0000007f, 0x0000007f, 0x0000007f, 0x0000007f, 0x0000007f, \
  0x0000007f, 0x0000007f, 0x0000007f, 0x0000007f, 0x0000007f, 0x0000007f, 0x0000007f, 0x0000007f, \
  0x0000007f, 0x0000007f, 0x0000007f, 0x0000007f, 0x0000007f, 0x0000007f, 0x0000007f, 0x0000007f, \
  0x0000007f, 0x0000007f, 0x0000007f, 0x0000007f, 0x0000007f, 0x0000007f, 0x0000007f, 0x0000007f, \
  0x0000007f, 0x0000007f, 0x0000007f, 0x0000007f, 0x0000007f, 0x0000007f, 0x0000007f, 0x0000007f, \
  0x0000007f, 0x0000007f, 0x0000007f, 0x0000007f, 0x0000007f, 0x0000007f, 0x0000007f, 0x0000007f, \
  0x0000007f, 0x0000007f, 0x0000007f, 0x0000007f, 0x0000007f, 0x0000007f, 0x0000007f, 0x0000007f, \
  0x0000007f, 0x0000007f, 0x0000007f, 0x0000007f, 0x0000007f, 0x0000007f, 0x0000007f, 0x0000007f, \
  0x0000007f, 0x0000007f, 0x0000007f, 0x0000007f, 0x0000007f, 0x0000007f, 0x0000007f, 0x0000007f, \
  0x0000007f, 0x0000007f, 0x0000007f, 0x0000007f, 0x0000007f, 0x0000007f, 0x0000007f, 0x0000007f, \
  0x0000007f, 0x0000007f, 0x0000007f, 0x0000007f, 0x0000007f, 0x0000007f, 0x0000007f, 0x0000007f, \
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
  0x0000007f, 0x0000007f, 0x0000007f, 0x0000007f, 0x0000007f, 0x0000007f, 0x0000007f, 0x0000007f, \
  0x0000007f, 0x0000007f, 0x0000007f, 0x0000007f, 0x0000007f, 0x0000007f, 0x0000007f, 0x0000007f, \
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
}
