sbarry753/cse123/max78000_timbre_transfer/gusynth/weights.h

// This file was @generated automatically

#define BIAS_0 { \
  0x0a, 0x01, 0x0a, 0x00, 0x07, 0xf9, 0xf1, 0x14, 0xff, 0xfa, 0x03, 0xf7, 0x06, 0xfc, 0x04, 0x0a, \
  0xf9, 0x04, 0xf6, 0x09, 0xf7, 0x04, 0x05, 0x02, 0x08, 0xf8, 0x08, 0x06, 0x11, 0x08, 0x06, 0x0f, \
  0x03, 0xec, 0xf5, 0x0b, 0xf8, 0x0f, 0xf3, 0x09, 0xf0, 0xf8, 0xf2, 0x07, 0x00, 0xee, 0xf5, 0x0d, \
  0x1d \
}
#define KERNELS { \
  0x50180000, 0x0000006f, 0xdbd824db, 0xdb25f4de, 0x22f10107, 0x0e2a0419, 0x310b14ea, 0xfb2ce40c, \
  0x2ffb1609, 0xfbe606dc, 0xd803e903, 0xead7d7ee, 0xc3d516e9, 0xe1d7f910, 0xd624f803, 0x2504f52c, \
  0xfcfd3104, 0xe10607e5, 0xa4ea02bb, 0x071ee212, 0xfb17060f, 0x19040b1b, 0x06080dfb, 0x0000e80f, \
  0x16dc111e, 0x08112112, 0xff240ff7, 0xfbdbfffc, 0xd609ffe5, 0xfcf70efb, 0xf20c0407, 0x1ffb13fe, \
  0xf713fc06, 0x08110ce8, 0xf4f5f0e7, 0xf4e8fc0d, 0x0a07060f, 0x0df70913, 0x0f03f40a, 0x10ff0105, \
  0xf60b1610, 0x04000104, 0xfc0efce2, 0xe90de8e2, 0xfdf6e9fe, 0xe6f70dff, 0xf505fefc, 0x0500060a, \
  0x0af509fa, 0xf20606e2, 0xf604f00e, 0xf8e80ae8, 0xf20eeeee, 0x08d30204, 0x02d8f103, 0xe4010fed, \
  0x081b17f8, 0x0835fd02, 0x0f0125e5, 0xed28ee0f, 0xf1faf1df, 0xfe12eafe, 0x2102f919, 0x17f102fb, \
  0x03fefb07, 0xe90b0a01, 0x00f211f6, 0xfd09fbe3, 0x0cf7e714, 0x03e9e4f7, 0xd912f3ea, 0xf7f41503, \
  0x1314ffe6, 0x1c04eb16, 0xf71af0fe, 0x2ef1ef39, 0xfc0906f0, 0xef11fdf0, 0x16ffeed9, 0xf4e4d3f3, \
  0xefccd30a, 0xe810f2f5, 0x170de9f7, 0xff200ee3, 0xfc01ff0a, 0xf6f0d904, 0xf1f40403, 0xd108feff, \
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
  0x0000005d, 0x1702f708, 0x0af31005, 0xff17040c, 0x000dea03, 0xe8e7f4f4, 0xff0810ec, 0x040dff08, \
  0x02ea0400, 0xef1504ee, 0xfd0afd1c, 0x0bfb0a03, 0xef0f10fa, 0xfe06fc08, 0x12f4feea, 0xf6f9f3f6, \
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
}
