sbarry753/cse123/max78000_timbre_transfer/gusynth/sampledata.h

// This file was @generated automatically

#define SAMPLE_INPUT_0 { \
  0x824c64d1, 0x59f64042, 0x518f0afd, 0xb4dbcd8d, 0xe36b4349, 0x34a5cfe3, 0xdd02339e, 0x7dd22267, \
  0x6de54380, 0xc7286b7d, 0xcc0c5b22, 0xf53491df, 0x70b2f100, 0x115ff1de, 0xf1952677, 0x909872d5, \
  0xe83d7423, 0x9caf9e8b, 0x156ac0bc, 0x8ddef4d8, 0x22620ca2, 0x235d4c4c, 0x97d217c3, 0x19f449b3, \
  0x080d0f46, 0xb1256b2a, 0x63f49a34, 0x3b8ef31a, 0x5a3c01db, 0x6d1c3ad9, 0x5b5bc755, 0xa30cc89f, \
  0x89df84f0, 0x1b5cef89, 0x804c25bc, 0xf18c522b, 0x3a35881f, 0x38eae3ad, 0xf89c7ebe, 0x24899bad, \
  0x9be024c3, 0x8f4f11d0, 0xbcd5fe19, 0xf5001ef8, 0x58d58582, 0xeb189d52, 0x357e6ee8, 0x2e7379c7, \
  0x6ab2373e, 0x2d28b763, 0x90815238, 0x29ad3a54, 0xe9681fb0, 0x9823ea48, 0xb83d4791, 0x327dc0d7, \
  0x4526d91a, 0xfd6fc8d7, 0xa1064774, 0x4388ec18, 0xcfc8c751, 0x7c3537db, 0x7526fd45, 0x18fb4255, \
  0xe63ed152, 0xe3b9dd1f, 0xb327dc74, 0x7e24ccc0, 0xa4a29130, 0xf2ef5097, 0x0b5b14b9, 0xa432f489, \
  0x0c829701, 0x70e75d42, 0xe63e068d, 0xb08d4f4e, 0x3d848aa2, 0x5dfa0971, 0xc605b132, 0xaac912f6, \
  0x6ab08efe, 0x013dfc90, 0xcdb6d21e, 0x426b338c, 0x9a8e043e, 0xf172a770, 0x5bdb9a66, 0x54e20c65, \
  0xdb516db8, 0xbb395ee4, 0xef3d76c7, 0xa91b9313, 0xc76eb9fb, 0x7a68634e, 0x0858294b, 0xec5d6742, \
  0x05c5f05f, 0xbbf943f8, 0x3e468a1a, 0xf83a6784, 0x81ee5c71, 0x8b347480, 0xad2622fa, 0x7e06a558, \
  0x0b8197a8, 0xa9298af7, 0x55e63883, 0x2f4de333, 0xb96f3bac, 0xcbb8d4a6, 0x81e9cba0, 0x956253f2, \
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
  0x2b70ab63, 0xcc82a7ad, 0xf7bd95fa, 0x9867b4e9, 0x7d5137b2, 0xcef0600a, 0x45123bab, 0x84214b39, \
  0xf7940d1f, 0x512d94b7, 0x23c0850b, 0x2af1b748, 0x88164e0b, 0x938e8666, 0x02ff1ecb, 0x2f9ef48b, \
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
}
