sbarry753/cse123/special_effects/localtesting/fuzz_effect.h

#ifndef FUZZ_EFFECT_H
#define FUZZ_EFFECT_H
#pragma once
#include <cmath>

// Declare the fuzz function so other files can see it
float processFuzz(float inputSample, float gain);

inline float processFuzz(float inputSample, float amount) {
    float driven = inputSample * amount;

    // Uses fminf/fmaxf which translate to single-cycle ARM hardware instructions
    return std::fmaxf(-1.0f, std::fminf(driven, 1.0f));
}

#endif // FUZZ_EFFECT_H
