sbarry753/cse123/special_effects/localtesting/wavefolding_effect.h

#pragma once
#include <cmath>

#pragma once
#include <cmath>

inline float processWavefolding(float inputSample, float gain) {
   float folded = inputSample * gain;
    
    // 2. Fold the signal back on itself if it crosses 1.0 or -1.0
    while (folded > 1.0f || folded < -1.0f) {
        if (folded > 1.0f) {
            // If it goes over 1.0, mirror it back down
            folded = 2.0f - folded;
        } else if (folded < -1.0f) {
            // If it goes under -1.0, mirror it back up
            folded = -2.0f - folded;
        }
    }
    
    // 3. Drop the volume safely for output
    return folded * 0.5f; 
}
